jerabaul29/LoggerWavesInIce_InSituWithIridium/DevelopmentCode/PowerControl_commitb76f6a5/PNGs/IMG_20170727_132701.jpg

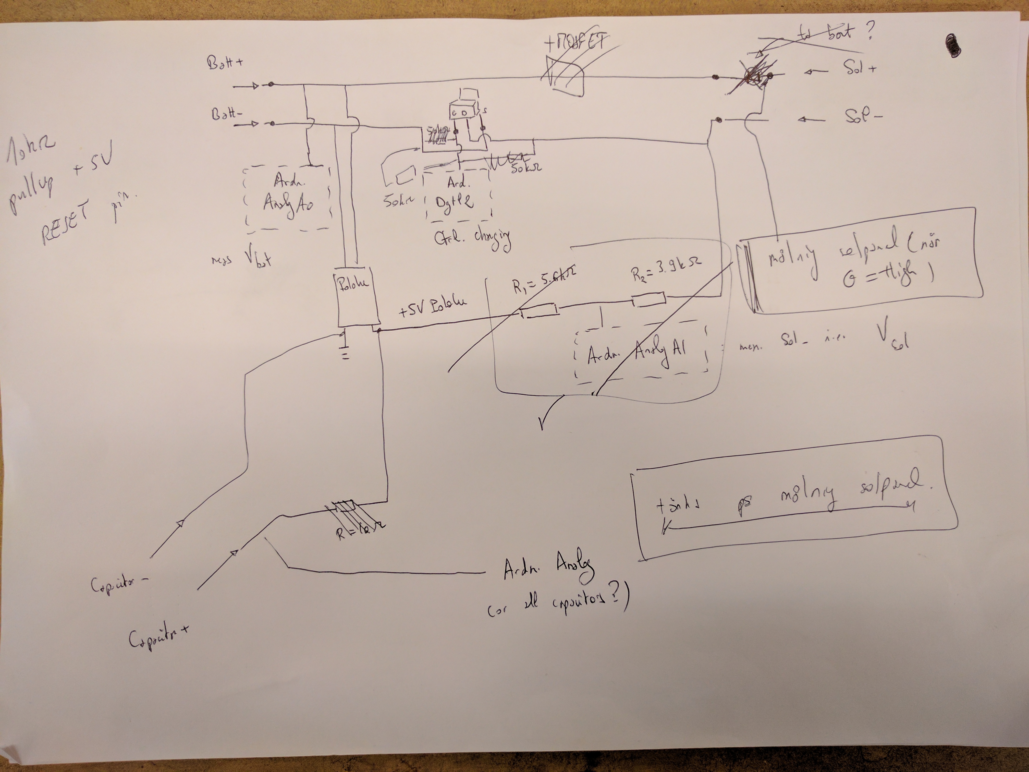
DevelopmentCode/PowerControl_commitb76f6a5/PNGs/IMG_20170727_132701.jpg
