jerabaul29/LoggerWavesInIce_InSituWithIridium/DevelopmentCode/PowerControl/parameters.h

/*

  *
  * The parameters for the power controlling mController
  * Should make sure all the parameters are good, in particular number of cycles
  * before uploading.
  *

Copyright (c) 2015 Jean Rabault jean.rblt@gmail.com

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
*/

#ifndef PARAMETERS
#define PARAMETERS

// TODO: implement the debugging in the classes
#define DEBUG false  // if DEBUG is true, Serial will be activated and used for logging information strings
#define SERIAL_DEBUG Serial
#define SHOW_LED false  // if SHOW_LED is true, the LED will be used for helping debugging

#define PIN_MSR_BAT A0      // measure of battery
#define PIN_MSR_SOL A1      // measure of solar panel on anode

#define ALPHA 0.41          // R_2 / (R_1 + R_2) in voltage divider

#define PIN_MFT_SOL 2      // command mosfet solar panel / battery
#define PIN_FBK_MGA 3      // feedback from Mega
#define PIN_MFT_MGA 4      // command mosfet giving to the Mega
#define PIN_CMD_LED 13     // command of intern LED

#define BAT_FULL_V 3.6  // threshold for full battery
#define BAT_EMPTY_V 2.8     // threshold for empty battery
#define MIN_MARGIN_PANEL 0.5  // minimum over voltage panel vs battery for it to be worth connecting

// number of cycles for which the microcontroller taking care of power sleeps
// each sleep cycle is 8s
// PRODUCTION VALUE ------------------------
// for production: 5 cycles is 40 seconds
// this means that every 40s, the mC will wake up, take care of solar power,
// take care of the Mega.
// TEST VALUE ------------------------------
// for tests: 2 cycles, will take care of solar power + Mega each 16 s
// 
#define CYCLES_DEEP_SLEEP 5  // production value
// #define CYCLES_DEEP_SLEEP 2  // test value

// number of loop () cycles before trying to wake up the Mega after is has been set asleep
// or refused to wake up.
// the duration of a loop() cycle is mostly determined by CYCLES_DEEP_SLEEP
// PRODUCTION VALUE -----------------------------
// ie if for production deep sleep is 5 cycles ie 40s, and CYCLES_BEFORE_MEGA_WAKEUP is 30,
// then the Mega will get the possibility to be waken up every 40s * 30  = 1200s = 20 minutes
// and the Mega can decide to be always awake (never stop asking current), or to perform measurements
// every 20 minutes (sleep one cycle), or every 40 minutes (sleep 2 cycles), etc.
// TEST VALUE -------------------------------------
// for tests, with value of 2: deep sleep is 2 cycles ie 16s, the Mega will get the possibility to
// wake up every 16s * 2 = 32s
// 
#define CYCLES_BEFORE_MEGA_WAKEUP 30  // production value
// #define CYCLES_BEFORE_MEGA_WAKEUP 2 // test value

#endif
