jerabaul29/LoggerWavesInIce_InSituWithIridium/DevelopmentCode/ArduinoMega_commit6cec5acdf/src/GPSManager.cpp

#include "GPSManager.h"

// TODO:
// fully use the Adafruit GPS class instead of doing some parsing by hand.
// this may request spending some time looking at their library

GPSManager::GPSManager(HardwareSerial * serial_port_gps, SDManager * sd_manager):
  serial_port_gps(serial_port_gps),
  sd_manager(sd_manager),
  GPS_rx_buffer_position(0),
  instance_GPS(Adafruit_GPS{serial_port_gps}),
  current_n_read_GPS(0)
{
}

void GPSManager::start(void){
    PDEBMSG("GPS start")

    delay(250);

    instance_GPS.begin(9600);
    delay(10);

    // uncomment this line to turn on RMC (recommended minimum) and GGA (fix data) including altitude
    instance_GPS.sendCommand(PMTK_SET_NMEA_OUTPUT_RMCGGA);
    // uncomment this line to turn on only the "minimum recommended" data
    // instance_GPS.sendCommand(PMTK_SET_NMEA_OUTPUT_RMCONLY);

    // Set the update rate
    instance_GPS.sendCommand(PMTK_SET_NMEA_UPDATE_1HZ);   // 1 Hz update rate
    instance_GPS.sendCommand(PMTK_API_SET_FIX_CTL_1HZ);

    // Request updates on antenna status, comment out to keep quiet
    // instance_GPS.sendCommand(PGCMD_ANTENNA);

    delay(1000);

    wdt_reset();

    this->clean_incoming_buffer();
}

void GPSManager::perform_logging(void){
  // while any chars incoming, grab them
  while (serial_port_gps->available() > 0){
    // if reach the end of a message, post it
    int len = this->catch_message();
    if(len > 0){
      sd_manager->post_on_SD_card(GPS_rx_buffer, len);
    }
  }
}


int GPSManager::catch_message(void){
  while (serial_port_gps->available()>0){

    char c_GPS = instance_GPS.read();

    if (c_GPS=='\n'){
      int swp = GPS_rx_buffer_position;
      GPS_rx_buffer_position = 0;
      return(swp);
    }
    else{
      // if enough space on the buffer, log
      if (GPS_rx_buffer_position < SIZE_GPS_BUFFER){
        // just save on the buffer if enough space
        GPS_rx_buffer[GPS_rx_buffer_position] = c_GPS;
        GPS_rx_buffer_position += 1;
      }
      // if not enough space, ask to do something anyway
      else{
        GPS_rx_buffer_position = 0;
        return(GPS_rx_buffer_position);
      }
    }
  }

  return(0);
}

int GPSManager::load_gprmc_message(){
  int crrt_length_message;

  this->clean_incoming_buffer();

  current_n_read_GPS = 0;

  // limit the maximum number of attempts
  while (current_n_read_GPS < MAX_NUMBER_ATTEMPTS_GPRMC){

    wdt_reset();

    // catch a complete message
    do{
      crrt_length_message = this->catch_message();
    }while(0 == crrt_length_message);

    // check if a GPRMC
    if ((GPS_rx_buffer[0] == '$') && (GPS_rx_buffer[1] == 'G') && (GPS_rx_buffer[2] == 'P') &&
        (GPS_rx_buffer[3] == 'R') && (GPS_rx_buffer[4] == 'M') && (GPS_rx_buffer[5] == 'C')) {

          // we have received one more GPRMC
          current_n_read_GPS += 1;

          // if valid, this is what we want
          if (GPS_rx_buffer[18] == 'A'){
            return(max(crrt_length_message, SIZE_GPS_BUFFER));
          }
    }
  }

  // if no valid message, at least return the last one
  return(crrt_length_message);
}

void GPSManager::clean_incoming_buffer(void){
  // flush current GPS buffer
  while (serial_port_gps->available() > 0) {
    serial_port_gps->read();
  }

  // then flush until the end of a message has arrived
  while (true){
    if (serial_port_gps->available() > 0){
      char crrt_char = serial_port_gps->read();
      if (crrt_char == '\n'){
        break;
      }
    }
  }

  // reset the GPS buffer position
  GPS_rx_buffer_position = 0;
}

const char * GPSManager::get_rx_buffer(void) const{
  return(GPS_rx_buffer);
}
