jerabaul29/LoggerWavesInIce_InSituWithIridium/DevelopmentCode/ArduinoMega_commit6cec5acdf/src/DebugMacros.cpp

#include "DebugMacros.h"

// template specializations get to the .cpp, otherwise linker is confused

/*
template<>
inline void debug_println (const char * data){
    // SERIAL_DEBUG.println(F("specialized template 1"));
    // SERIAL_DEBUG.println(F(data));
    SERIAL_DEBUG.println(F("specialized template 1"));
    SERIAL_DEBUG.println(F((String) data));
}
*/

/*
  To be used on strings: should be in the flash memory.
*/
void debug_println_string(const __FlashStringHelper * string_in){
    SERIAL_DEBUG.println(string_in);
}

/*
  To be used on strings: should be in the flash memory.
*/
void debug_print_string(const __FlashStringHelper * string_in){
    SERIAL_DEBUG.print(string_in);
}

void print_debug_status(void){
    // Debug
    PDEBMSG("Debug on " SHOW_VAR_NAME(SERIAL_DEBUG))

    // IMU
    PDEBMSG("IMU on " SHOW_VAR_NAME(SERIAL_VN100))

    // GPS
    PDEBMSG("GPS on " SHOW_VAR_NAME(SERIAL_GPS))

    // Iridium
    PDEBMSG("Iridium on " SHOW_VAR_NAME(SERIAL_IRIDIUM))
    #if USE_IRIDIUM
        PDEBMSG("using iridium for real")
    #else
        PDEBMSG("using iridium mock-up")
    #endif

    // Raspberry Pi
    PDEBMSG("Raspberry on " SHOW_VAR_NAME(SERIAL_RASPBERRY))
}
